Stylt1/audio-amp/img/Angle.backright.png

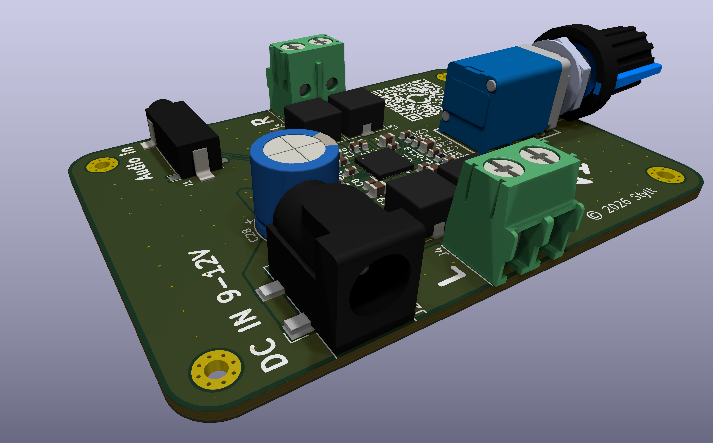
img/Angle.backright.png
