Stylt1/audio-amp/img/Angle.frontright.png

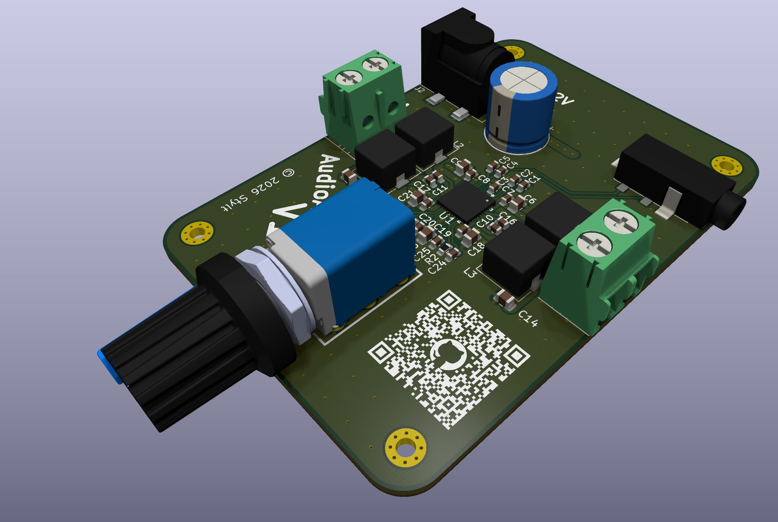
img/Angle.frontright.png
