Stylt1/audio-amp/img/F.Cu.png

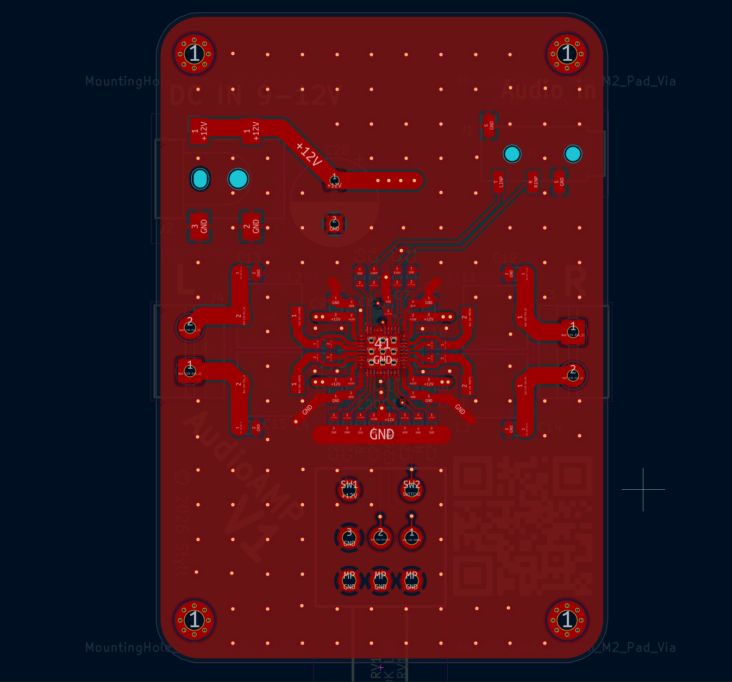
img/F.Cu.png
