Stylt1/audio-amp/img/In1.Cu.png

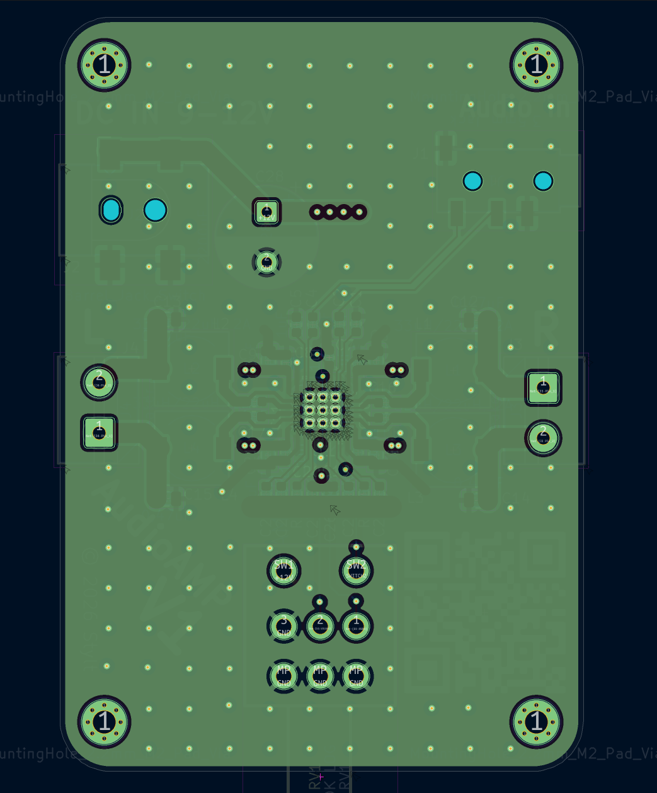
img/In1.Cu.png
