Stylt1/audio-amp/proof/Cart.png

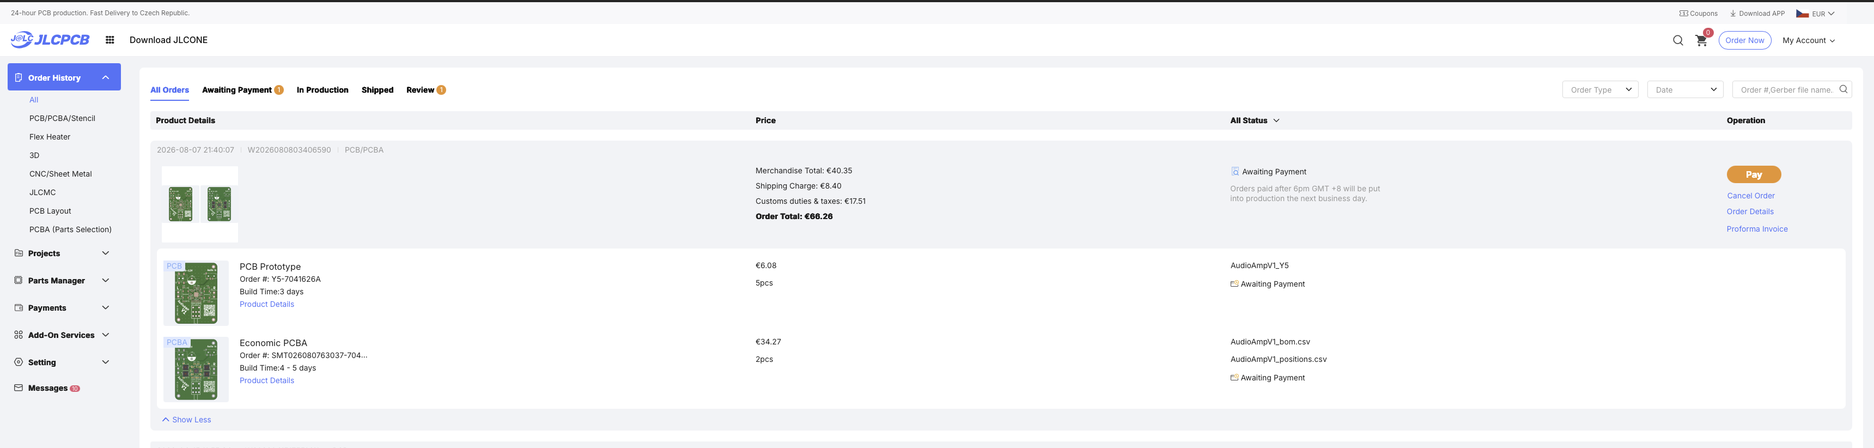
proof/Cart.png
