Stylt1/audio-amp/proof/Payment.png

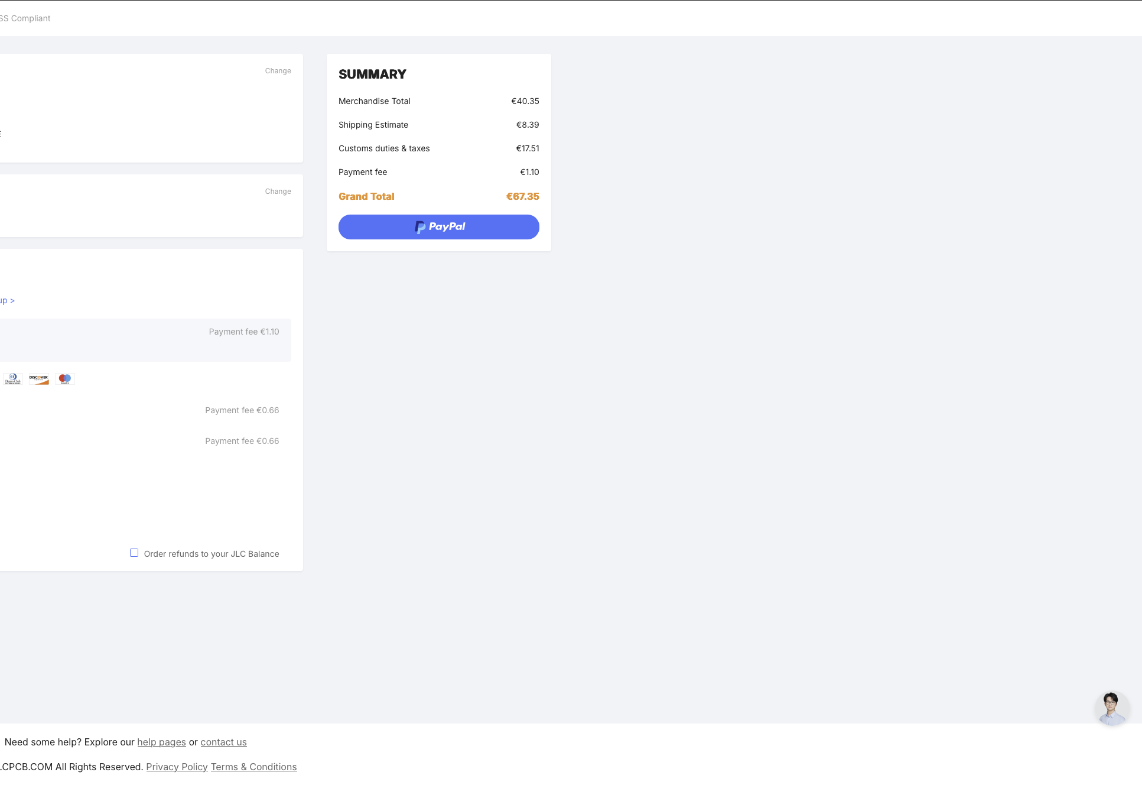
proof/Payment.png
