Stylt1/audio-amp/proof/PCBA.png

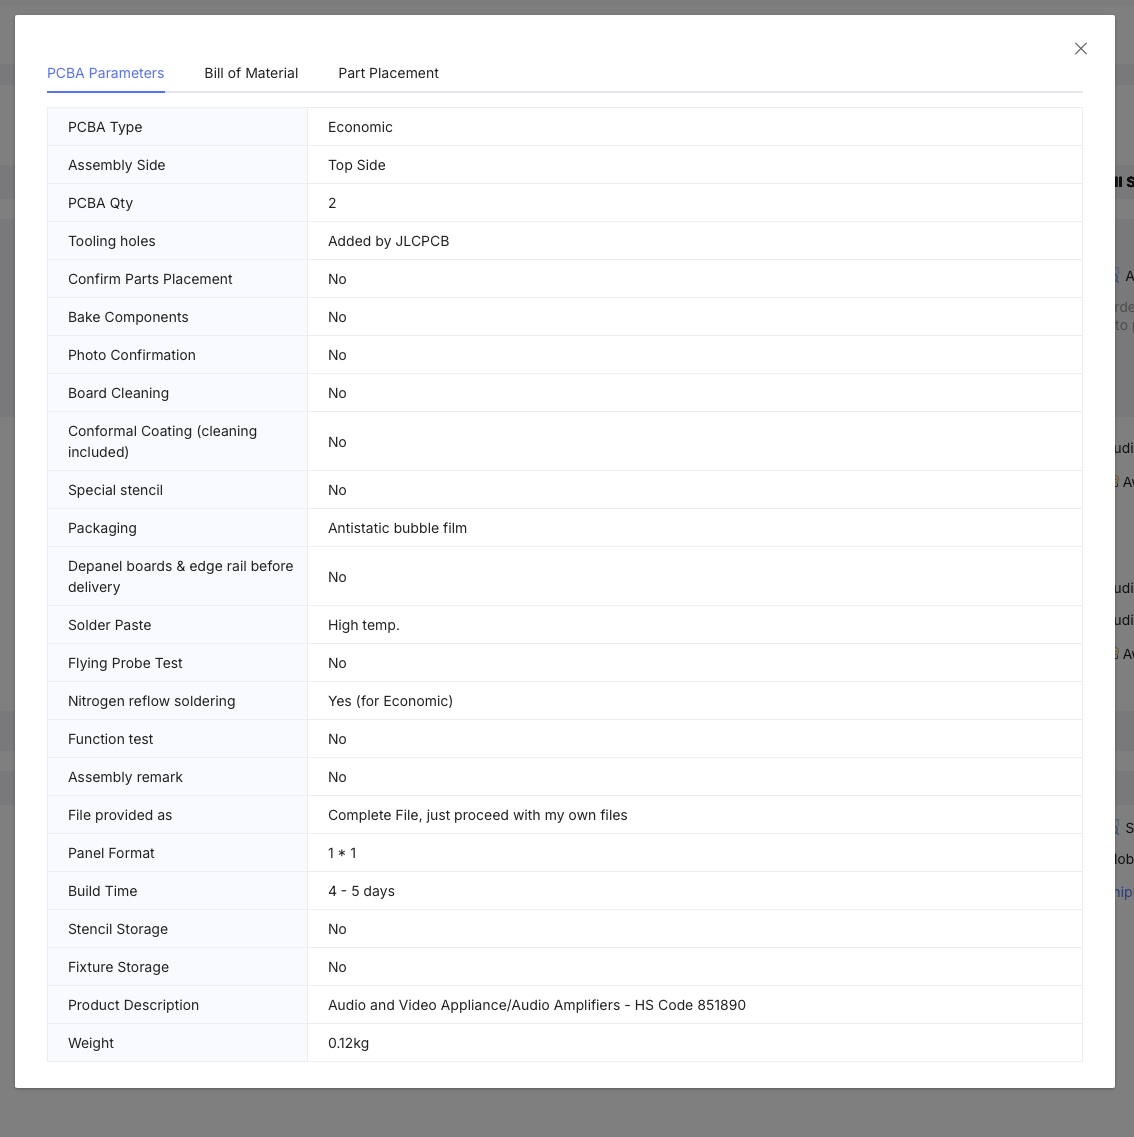
proof/PCBA.png
