Stylt1/audio-amp/proof/Components.png

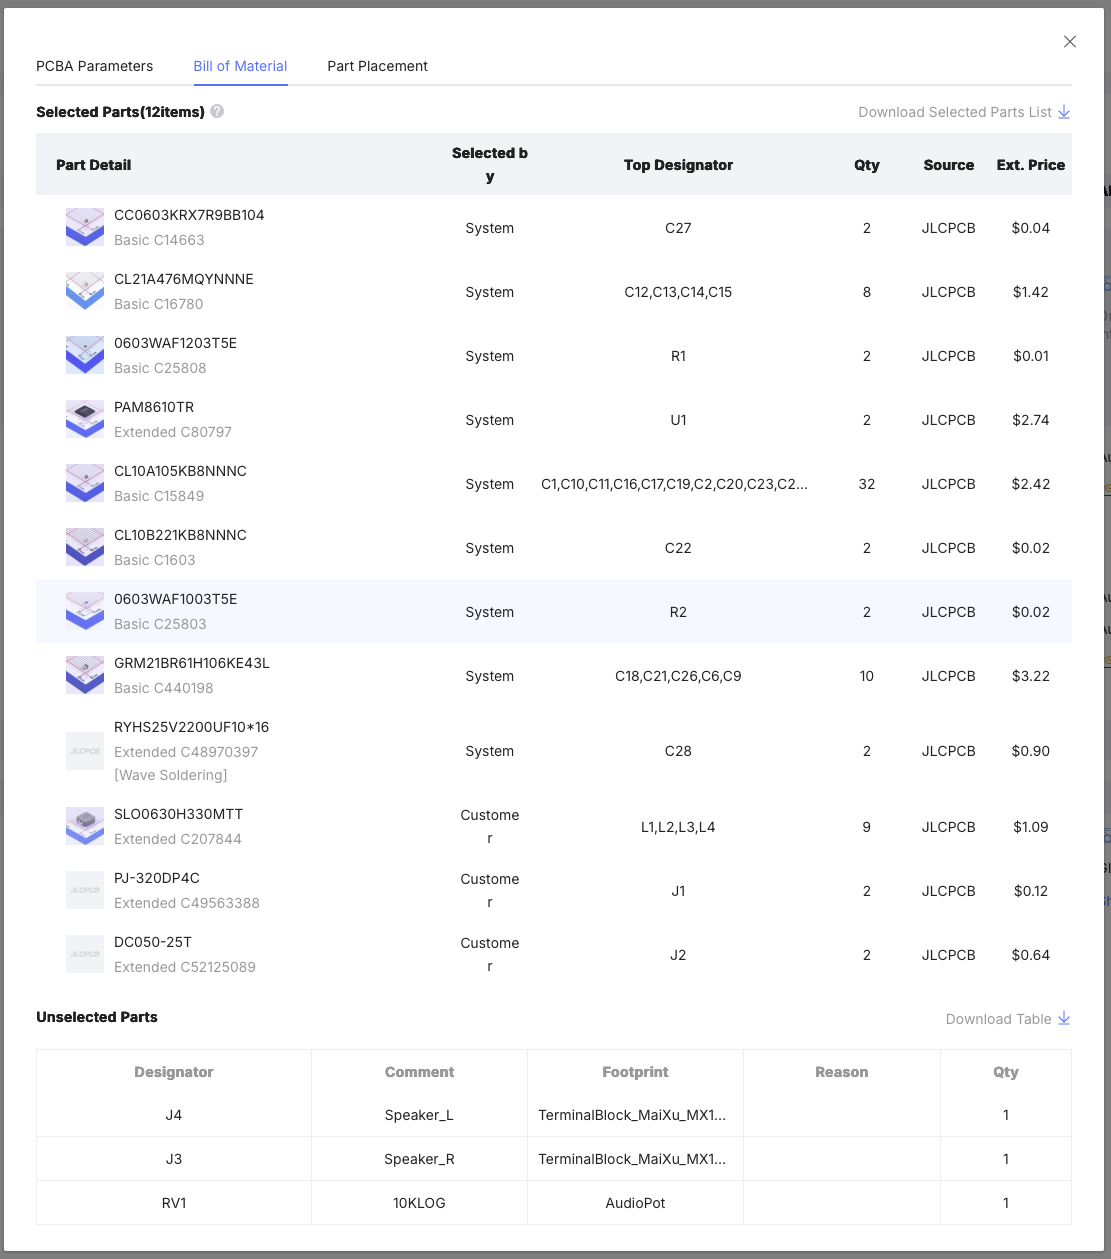
proof/Components.png
